garethnisbet/Fraction-Collection-Unit/Python/Images/BG2.png

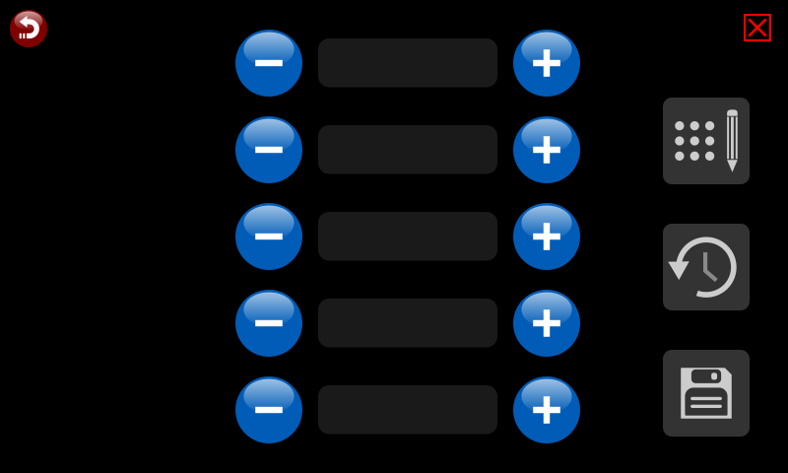
Python/Images/BG2.png
