garethnisbet/Fraction-Collection-Unit/Python/Images/BG3.png

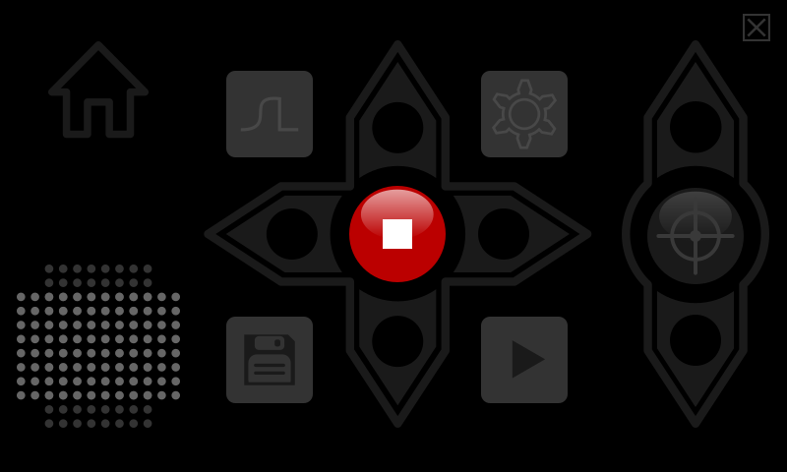
Python/Images/BG3.png
