garethnisbet/Fraction-Collection-Unit/Python/Images/BG5.png

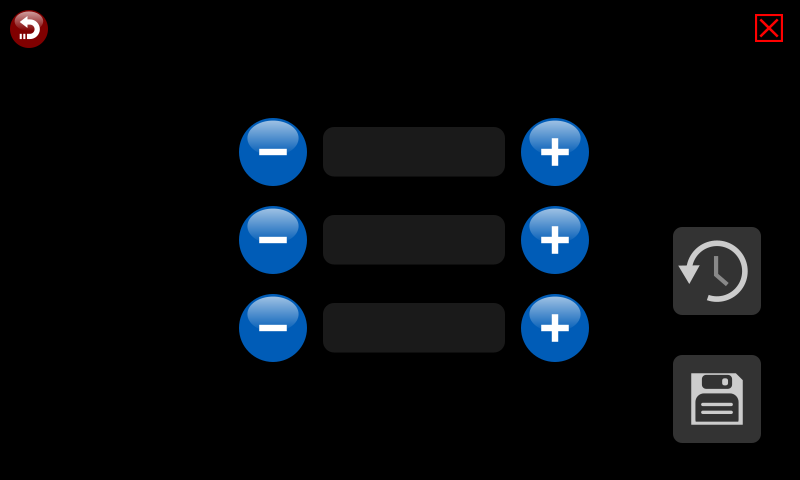
Python/Images/BG5.png
