garethnisbet/Fraction-Collection-Unit/Python/Images/BG.png

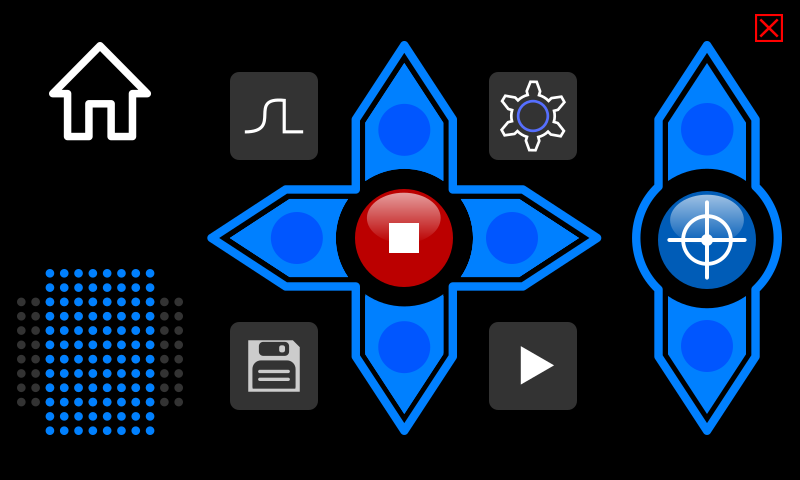
Python/Images/BG.png
