garethnisbet/Fraction-Collection-Unit/Python/Images/WellType1.png

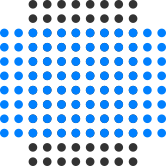
Python/Images/WellType1.png
