garethnisbet/Fraction-Collection-Unit/Python/Images/WellType2.png

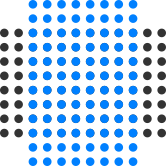
Python/Images/WellType2.png
