garethnisbet/Fraction-Collection-Unit/CAD/STL/Part_8_LargerClipTall_Right.stl

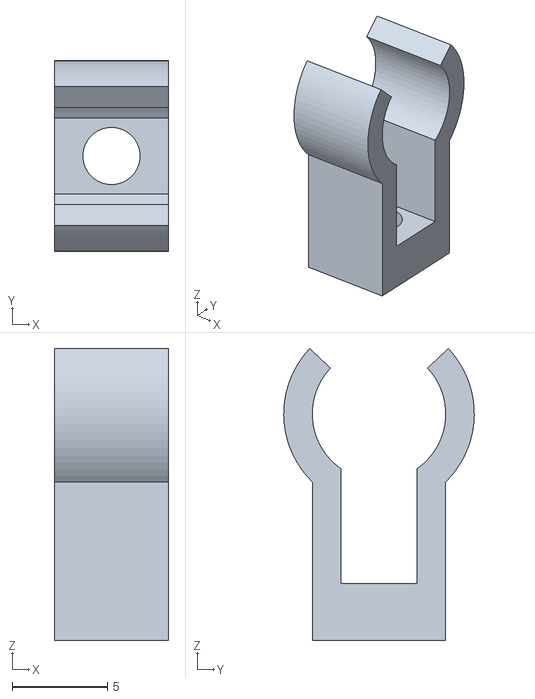
[picture p23: CAD file, 2024-01-13]
CAD/STL/Part_8_LargerClipTall_Right.stl
6.00 x 10.00 x 15.3
