garethnisbet/Fraction-Collection-Unit/CAD/STL/Part_7_Tall10mmClip_Right.stl

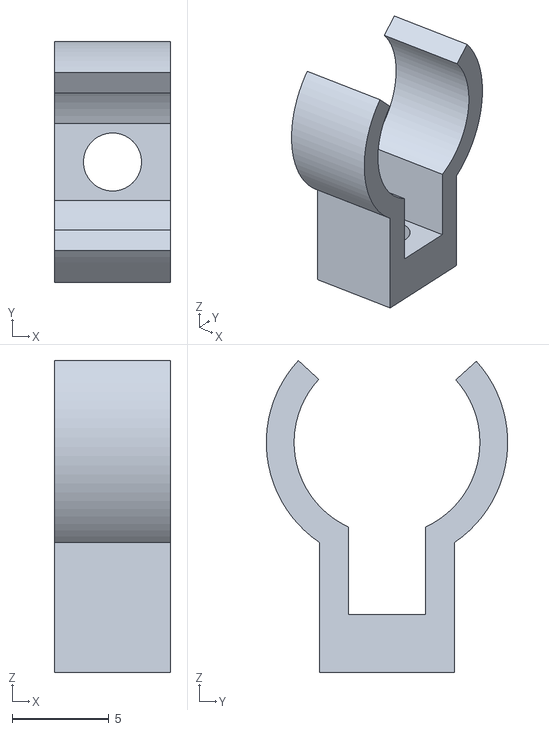
[picture p24: CAD file, 2024-01-13]
CAD/STL/Part_7_Tall10mmClip_Right.stl
6.00 x 12.5 x 16.1
