garethnisbet/Fraction-Collection-Unit/CAD/STL/Part_11_CableClamps.stl

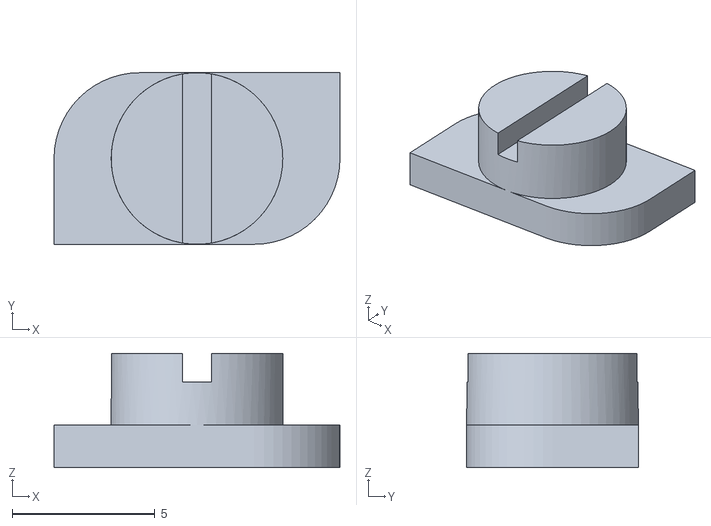
[picture p25: CAD file, 2024-01-13]
CAD/STL/Part_11_CableClamps.stl
10.0 x 6.00 x 4.00
