garethnisbet/Fraction-Collection-Unit/CAD/STL/Part_9_HexClip_Right.stl

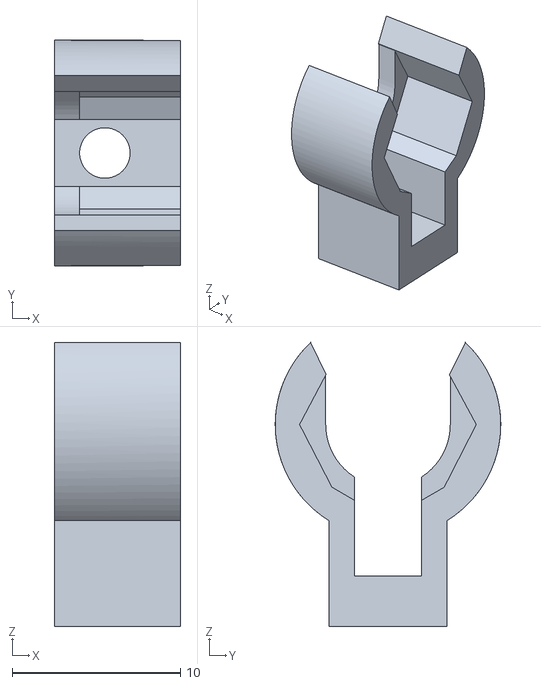
[picture p26: CAD file, 2024-01-13]
CAD/STL/Part_9_HexClip_Right.stl
7.50 x 13.4 x 16.9
