garethnisbet/Fraction-Collection-Unit/Instructions/CableTidyClip.png

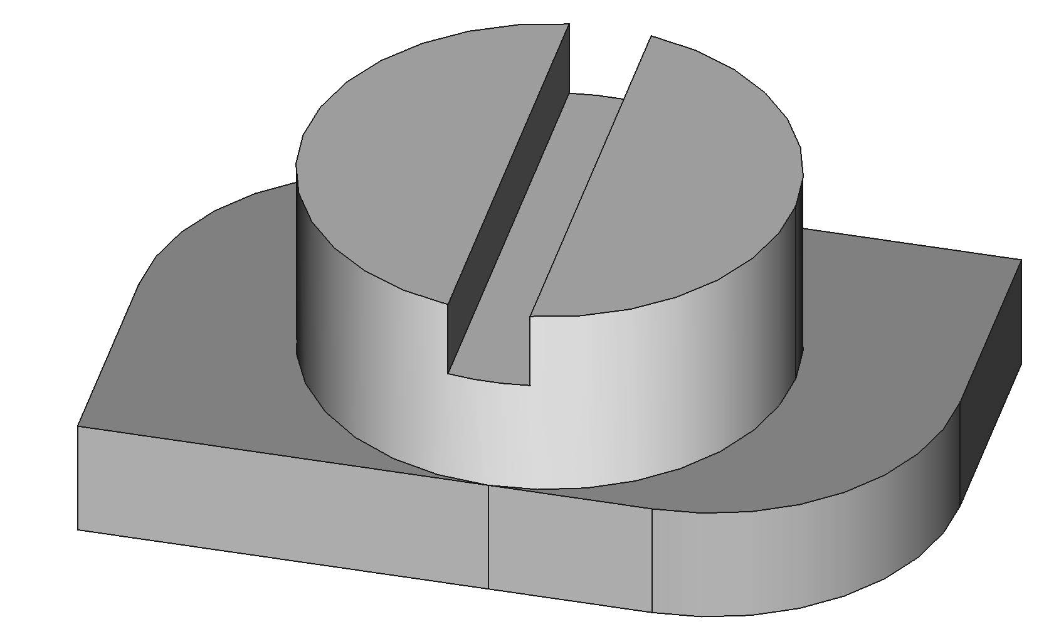
Instructions/CableTidyClip.png
