garethnisbet/Fraction-Collection-Unit/Instructions/CapillaryBracket.png

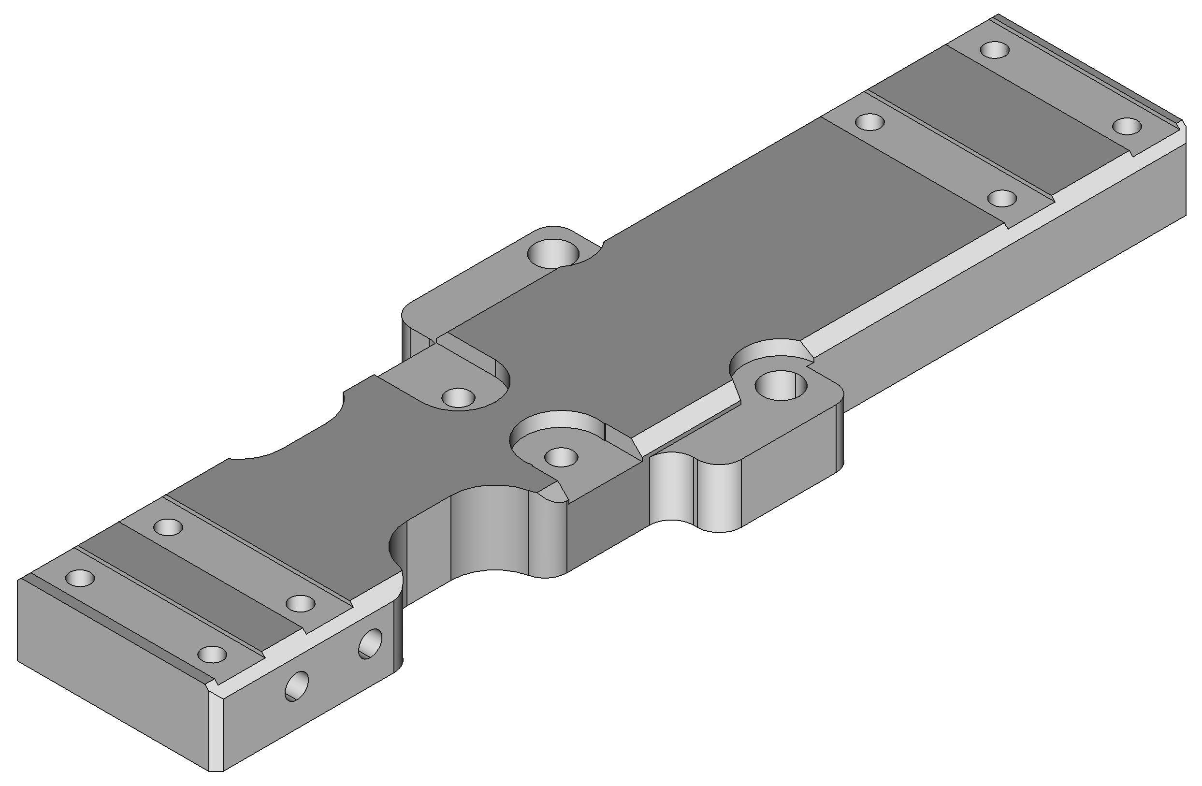
Instructions/CapillaryBracket.png
