garethnisbet/Fraction-Collection-Unit/Instructions/CapillaryStabiliser.png

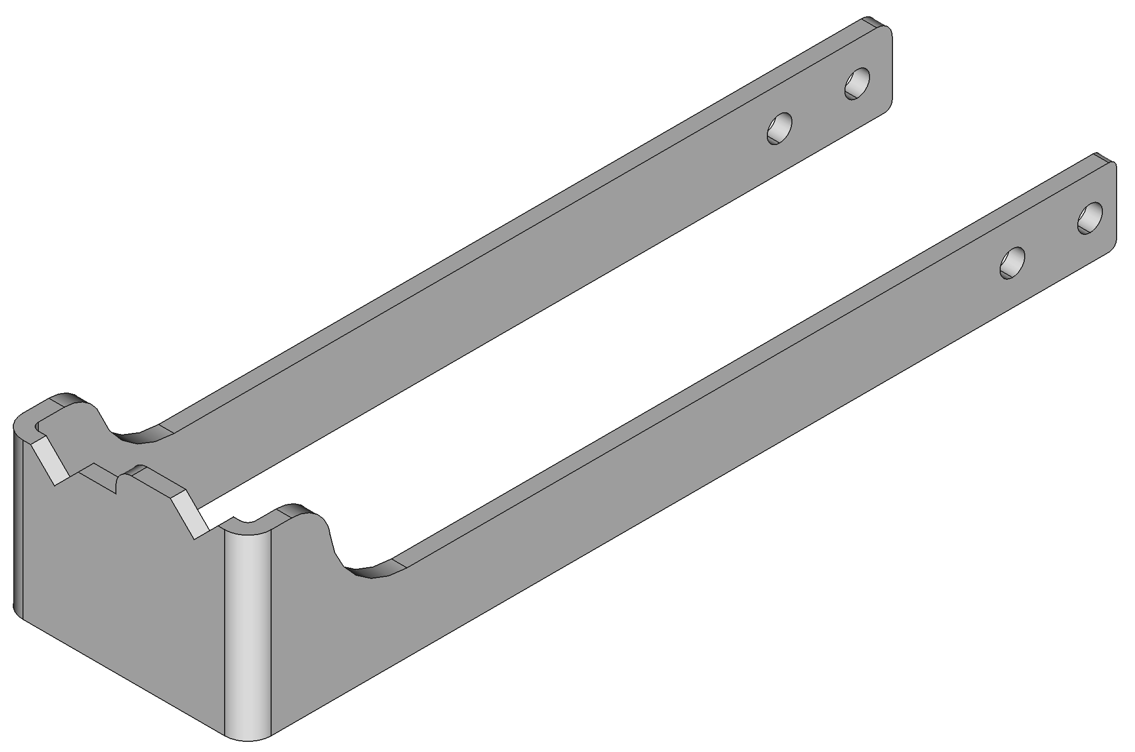
Instructions/CapillaryStabiliser.png
