garethnisbet/Fraction-Collection-Unit/Instructions/Clips.png

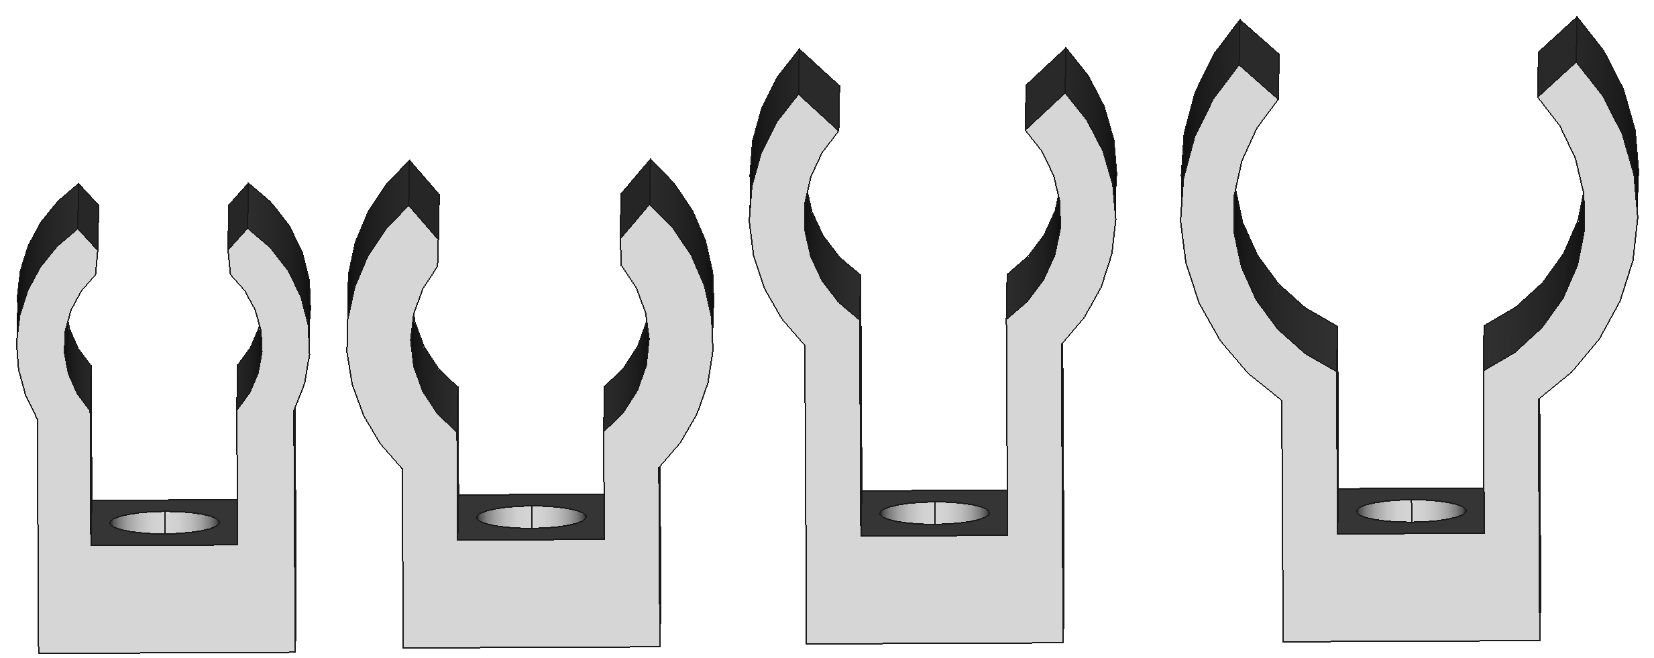
Instructions/Clips.png
