garethnisbet/Fraction-Collection-Unit/Instructions/IMG_20230724_181349.jpg

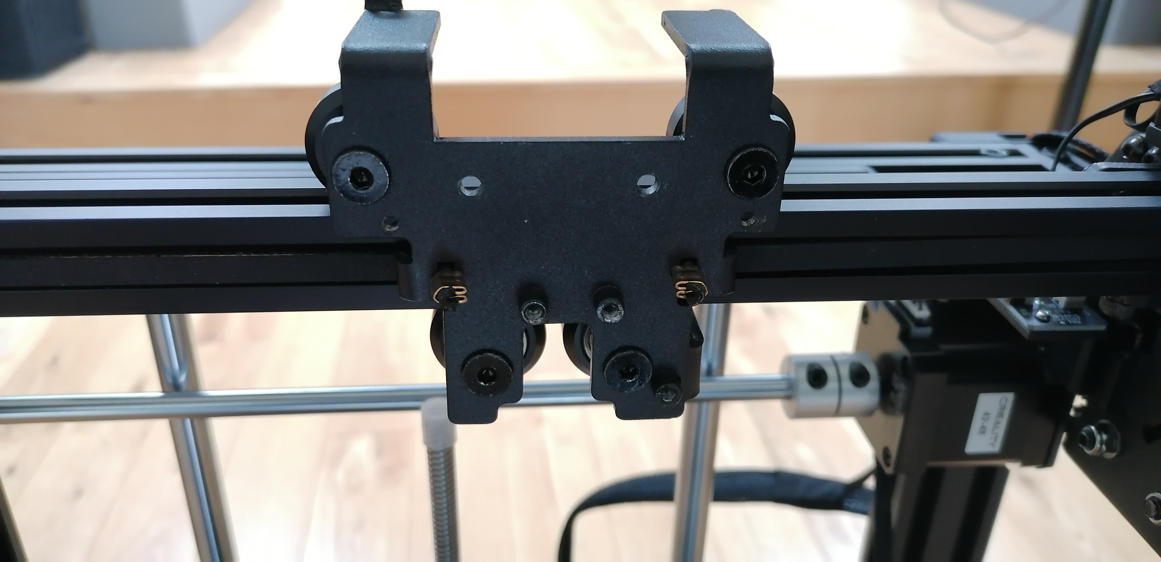
Instructions/IMG_20230724_181349.jpg
