garethnisbet/Fraction-Collection-Unit/Instructions/IMG_20230724_181405.jpg

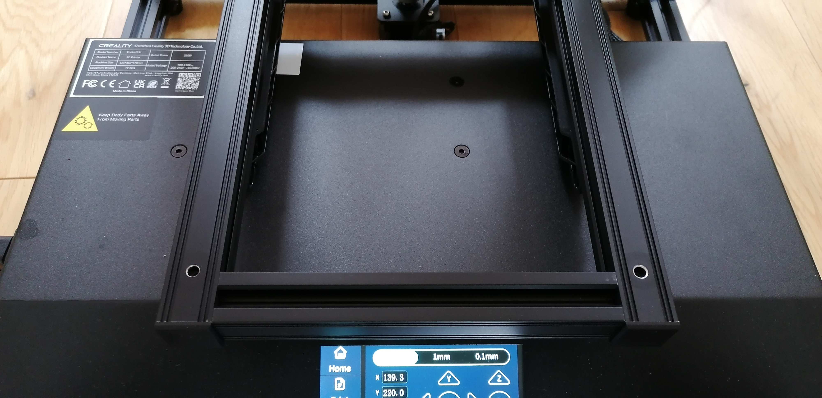
Instructions/IMG_20230724_181405.jpg
