garethnisbet/Fraction-Collection-Unit/Instructions/IMG_20231008_134917.jpg

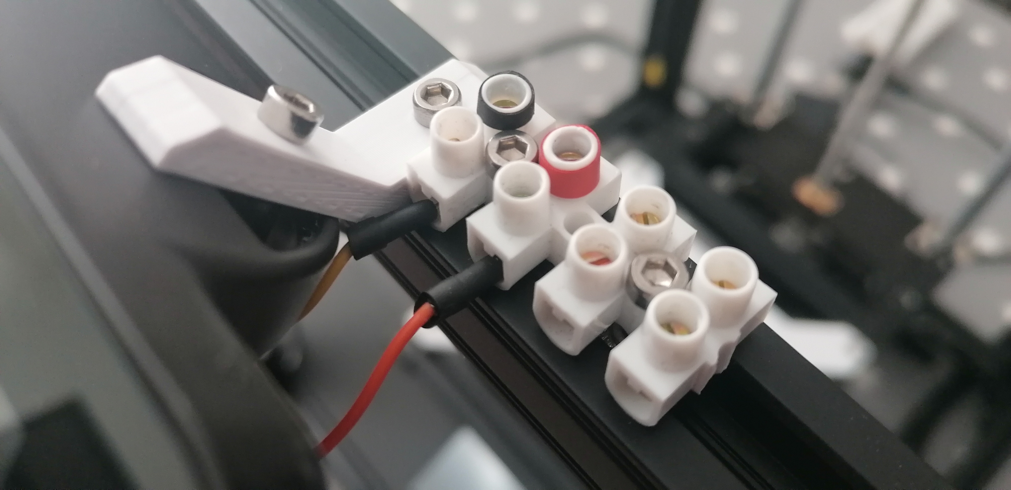
Instructions/IMG_20231008_134917.jpg
