garethnisbet/Fraction-Collection-Unit/Instructions/IMG_20231008_134955.jpg

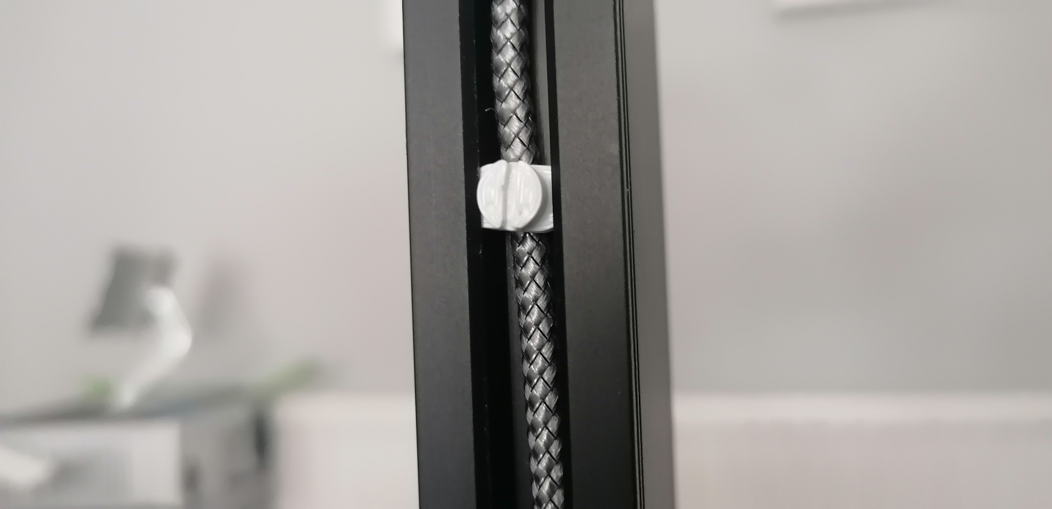
Instructions/IMG_20231008_134955.jpg
