garethnisbet/Fraction-Collection-Unit/Instructions/IMG_20231009_165750.jpg

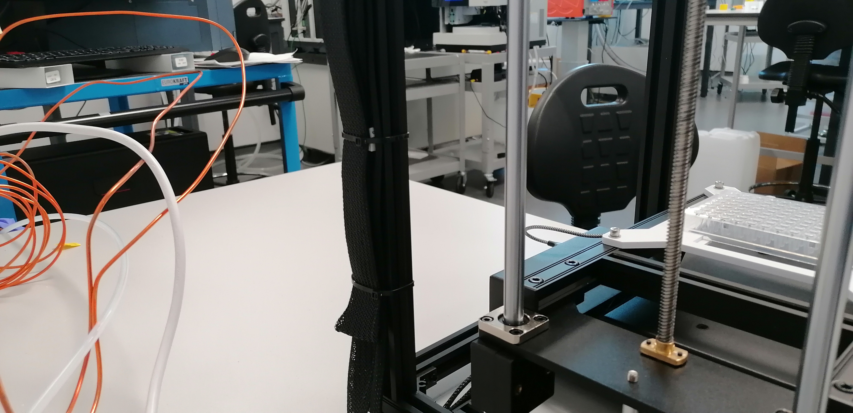
Instructions/IMG_20231009_165750.jpg
