garethnisbet/Fraction-Collection-Unit/Instructions/IMG_20231009_165756.jpg

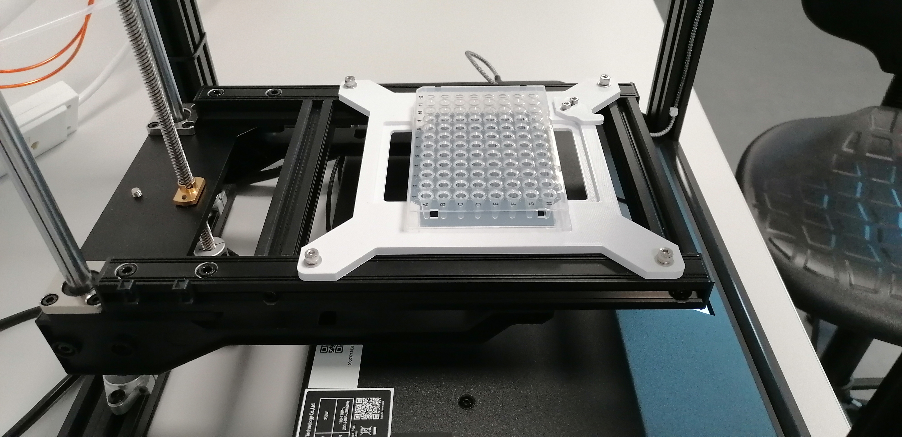
Instructions/IMG_20231009_165756.jpg
