garethnisbet/Fraction-Collection-Unit/Instructions/IMG_20231009_165801.jpg

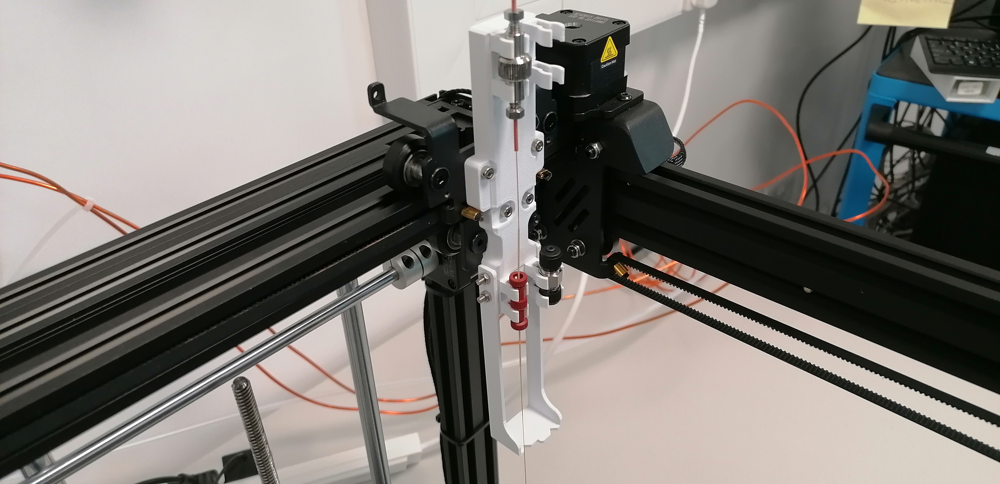
Instructions/IMG_20231009_165801.jpg
