garethnisbet/Fraction-Collection-Unit/Instructions/RetainingPlate.png

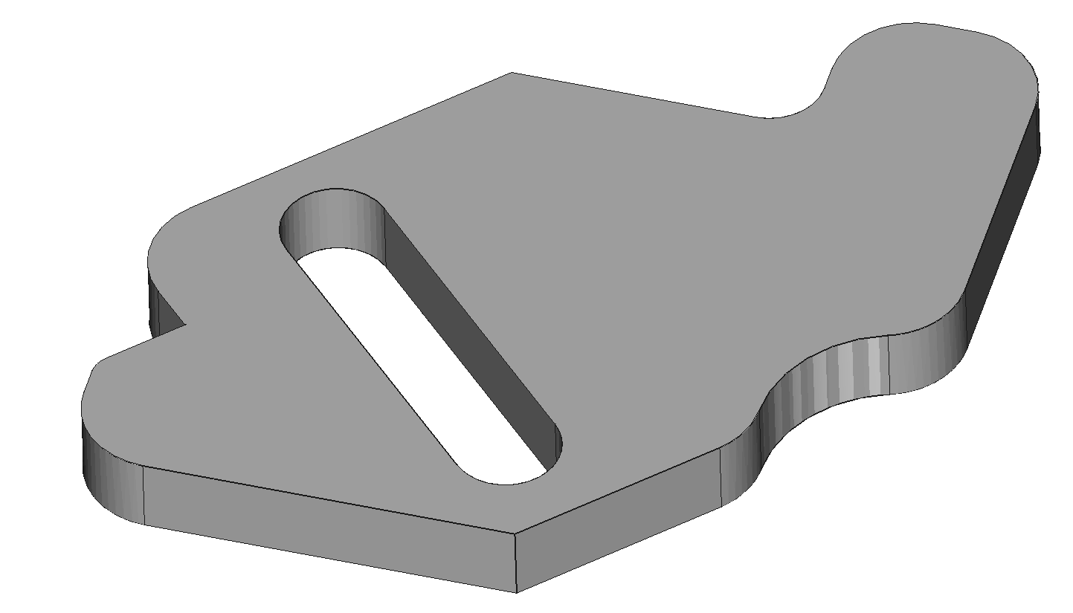
Instructions/RetainingPlate.png
