garethnisbet/Fraction-Collection-Unit/Instructions/S1.png

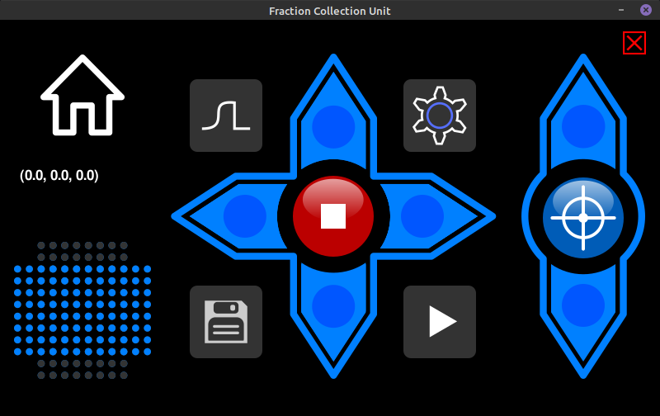
Instructions/S1.png
