garethnisbet/Fraction-Collection-Unit/Instructions/S2.png

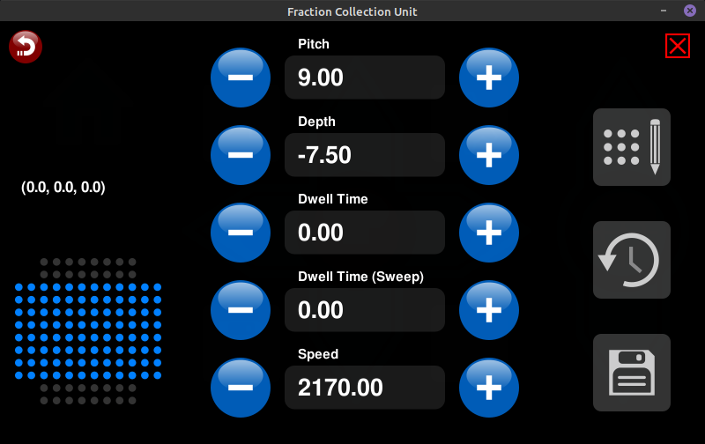
Instructions/S2.png
