garethnisbet/Fraction-Collection-Unit/Instructions/S3.png

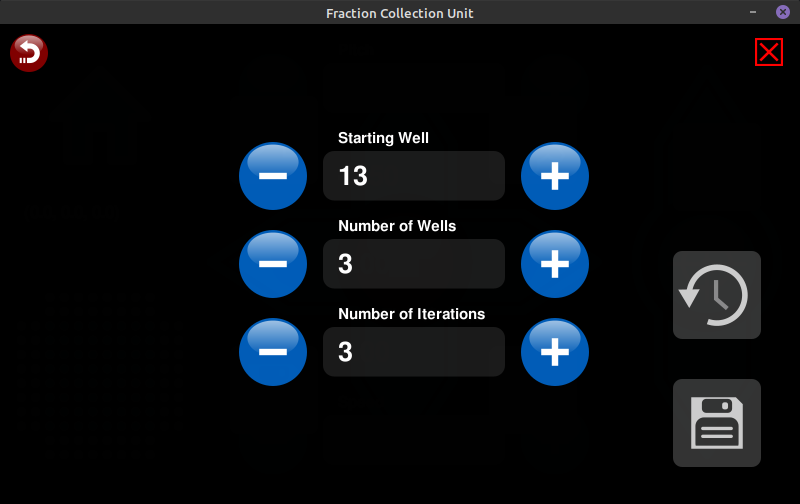
Instructions/S3.png
