garethnisbet/Fraction-Collection-Unit/Instructions/ScreenBracket.png

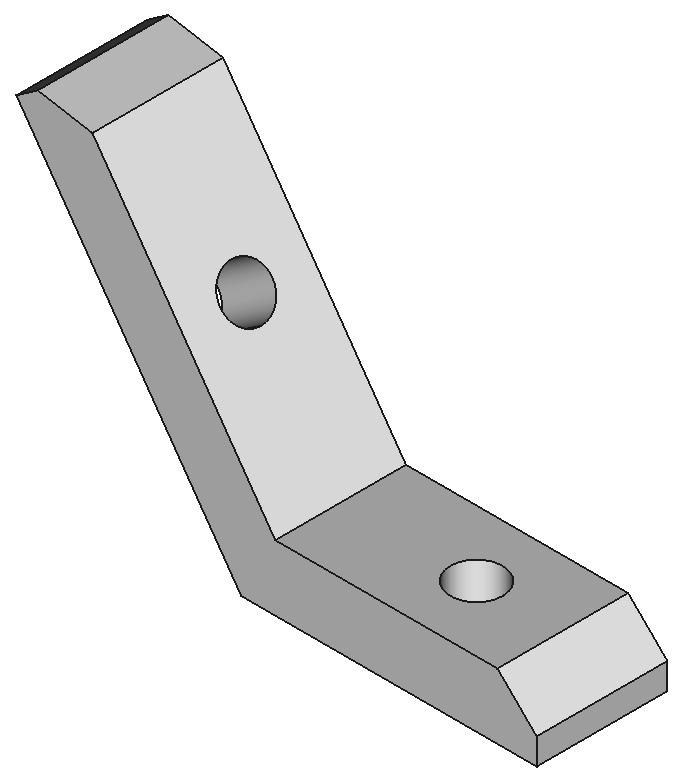
Instructions/ScreenBracket.png
